joshajohnson/vna/Hardware/Ecal/render.png

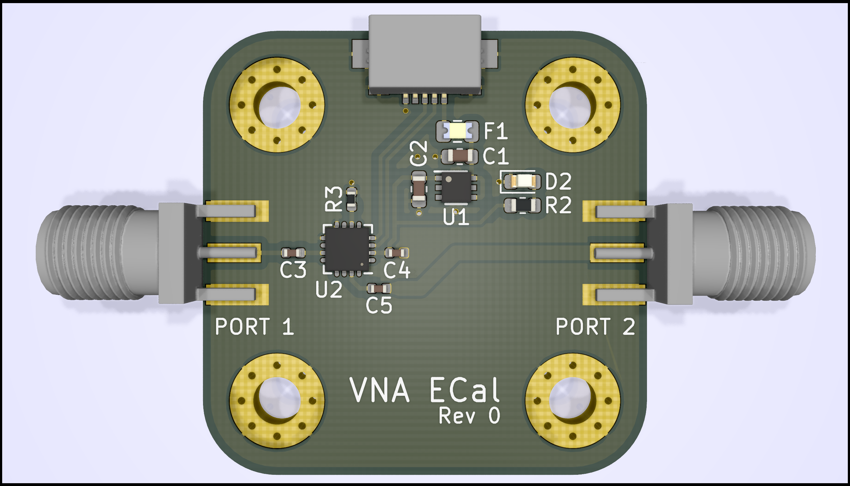
Hardware/Ecal/render.png
