joshajohnson/vna/Hardware/FrontPanel/render.png

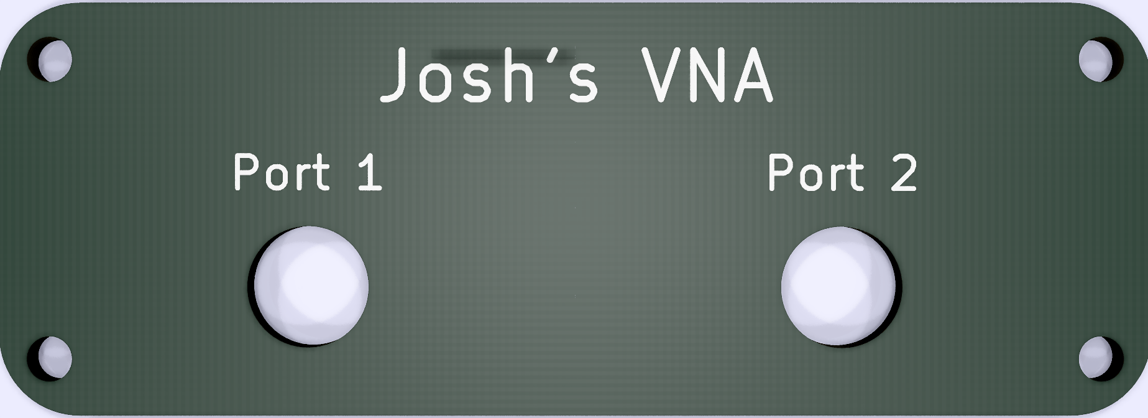
Hardware/FrontPanel/render.png
