joshajohnson/vna/Hardware/RearPanel/render.png

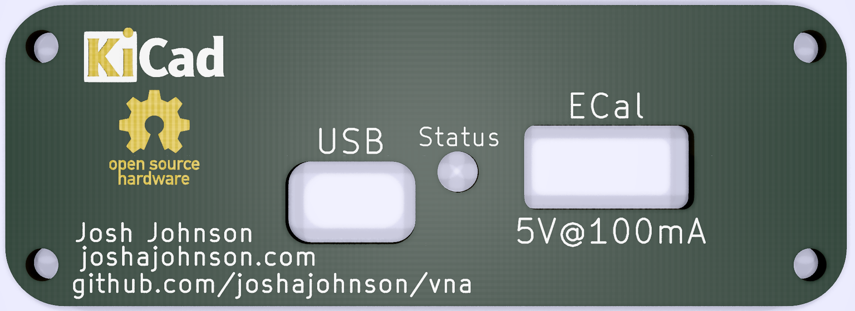
Hardware/RearPanel/render.png
