joshajohnson/vna/Hardware/VNA/svg/couplers-Directional Couplers.png

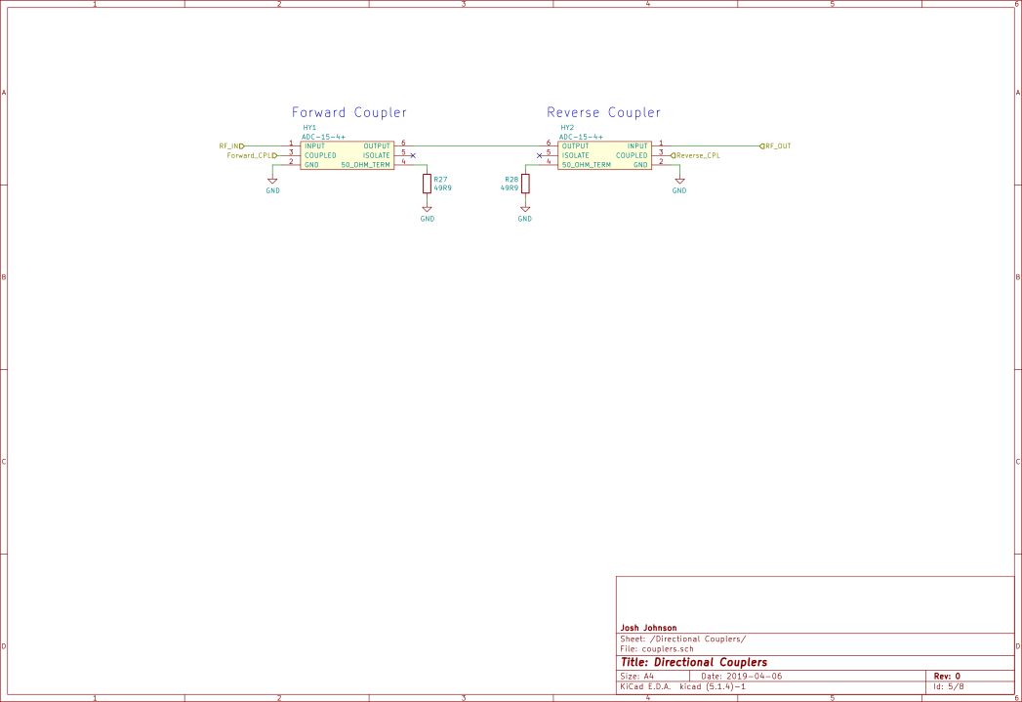
Hardware/VNA/svg/couplers-Directional Couplers.png
