joshajohnson/vna/Hardware/VNA/svg/filterBank-Filter Bank.png

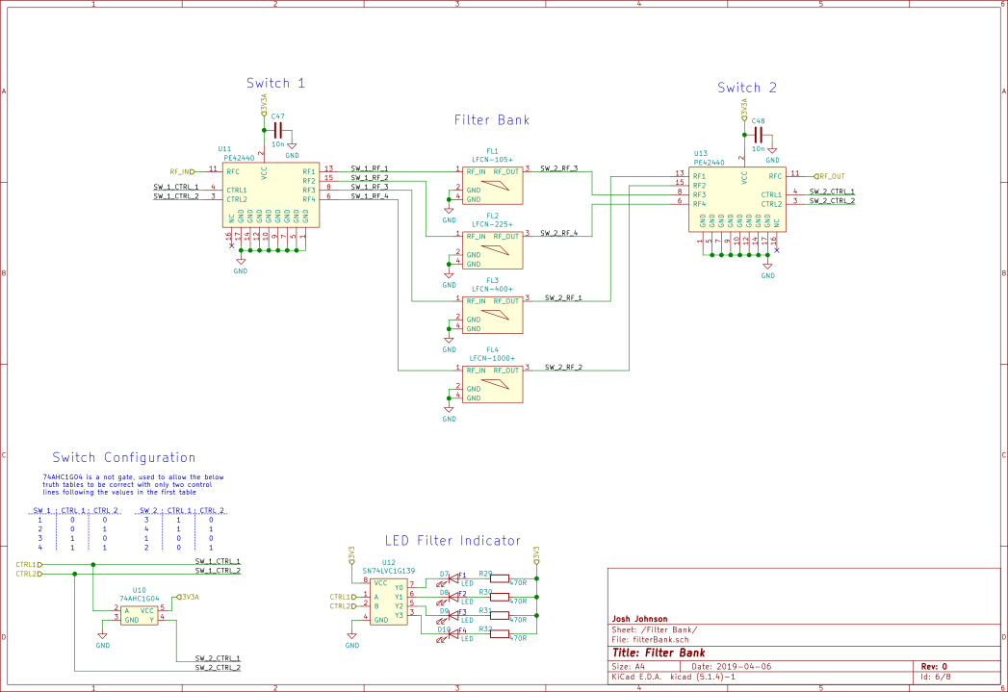
Hardware/VNA/svg/filterBank-Filter Bank.png
