joshajohnson/vna/Hardware/VNA/svg/gainPhaseDetect-Gain Phase Detection.png

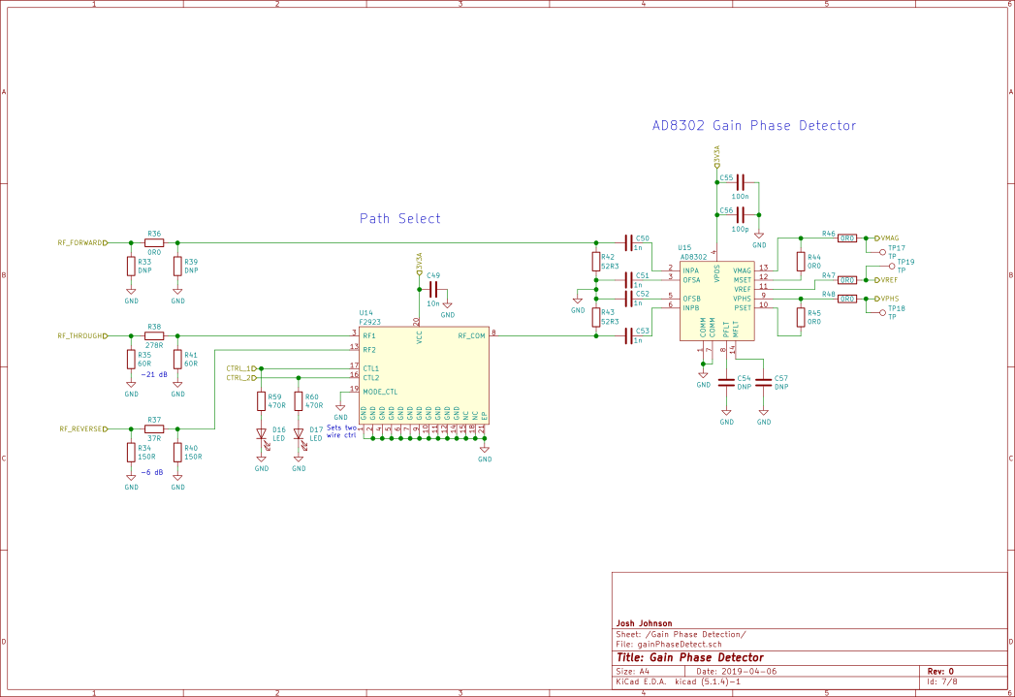
Hardware/VNA/svg/gainPhaseDetect-Gain Phase Detection.png
