joshajohnson/vna/Hardware/VNA/svg/microcontroller-Microcontroller.png

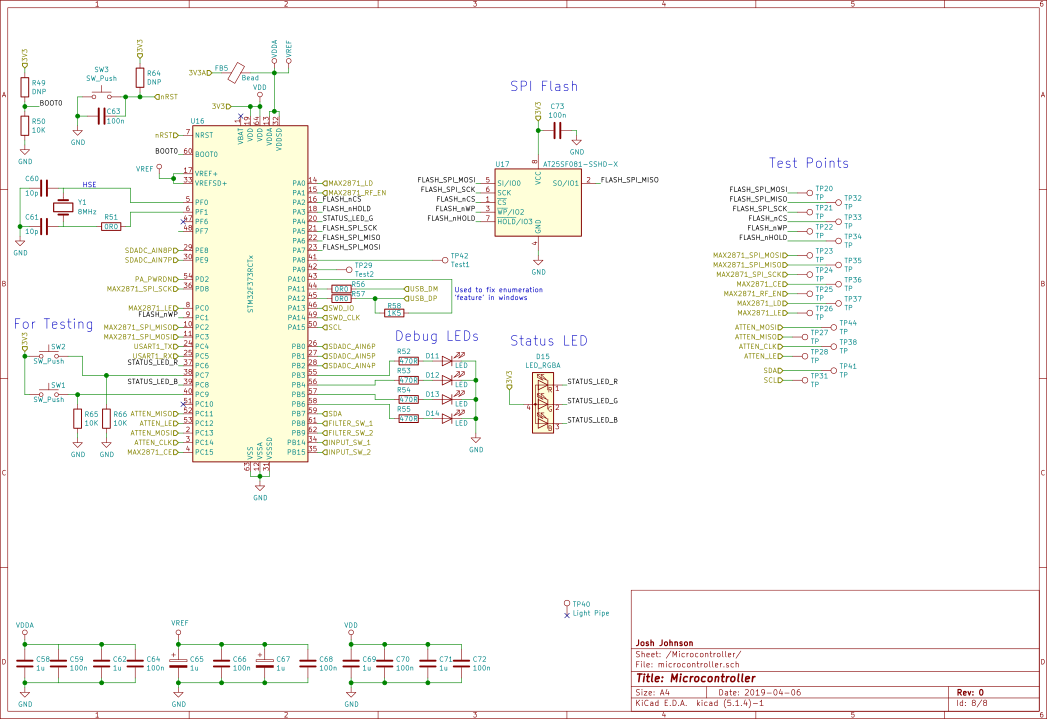
Hardware/VNA/svg/microcontroller-Microcontroller.png
