joshajohnson/vna/Hardware/VNA/svg/power-Power.png

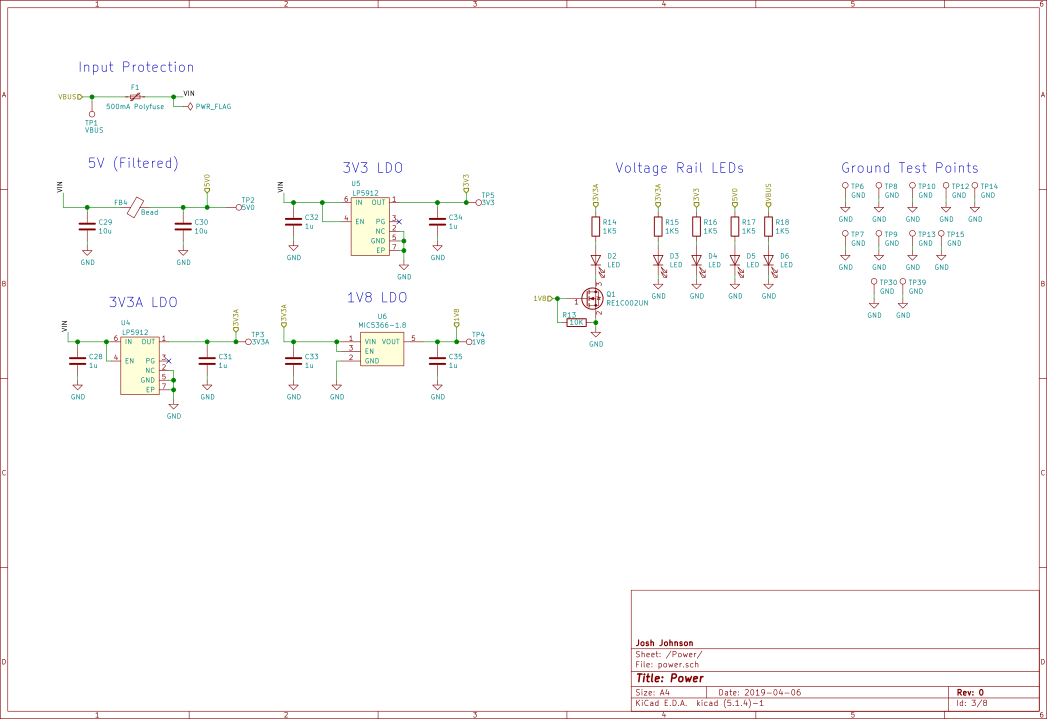
Hardware/VNA/svg/power-Power.png
