joshajohnson/vna/Hardware/VNA/svg/sourceLevel-Source Leveling.png

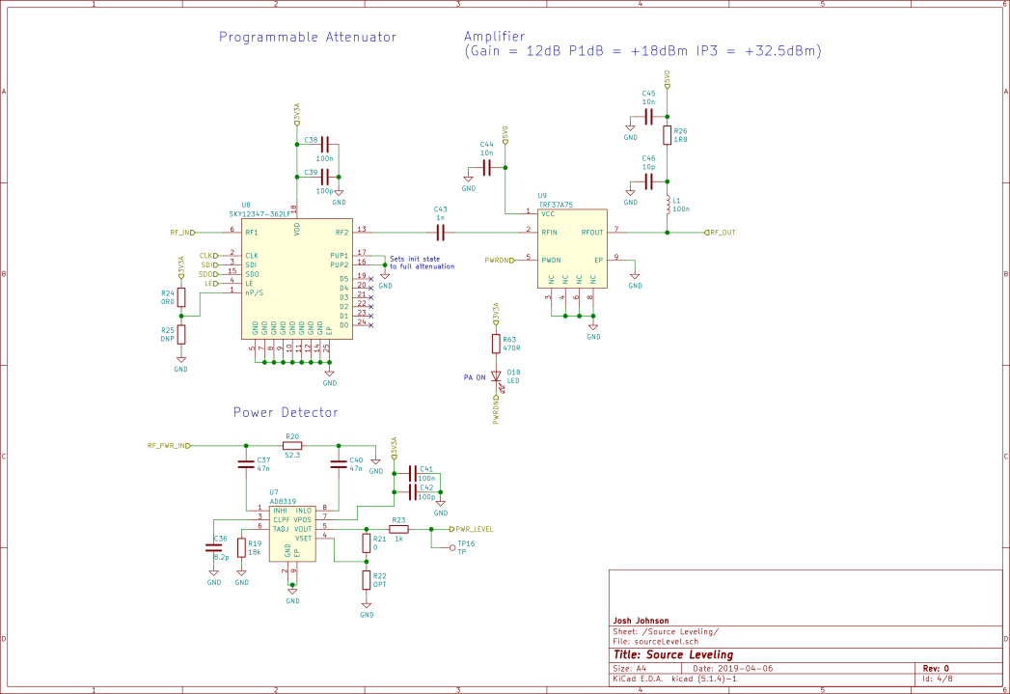
Hardware/VNA/svg/sourceLevel-Source Leveling.png
