joshajohnson/vna/Hardware/VNA/svg/synth-Synth.png

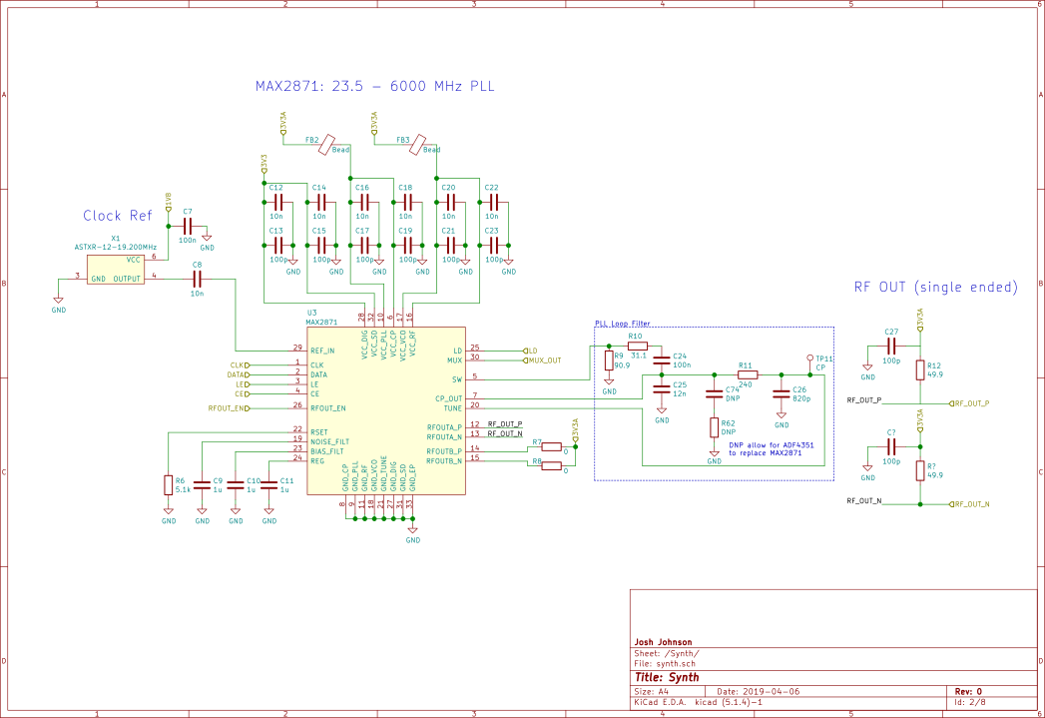
Hardware/VNA/svg/synth-Synth.png
