joshajohnson/vna/Hardware/VNA/svg/VNA.png

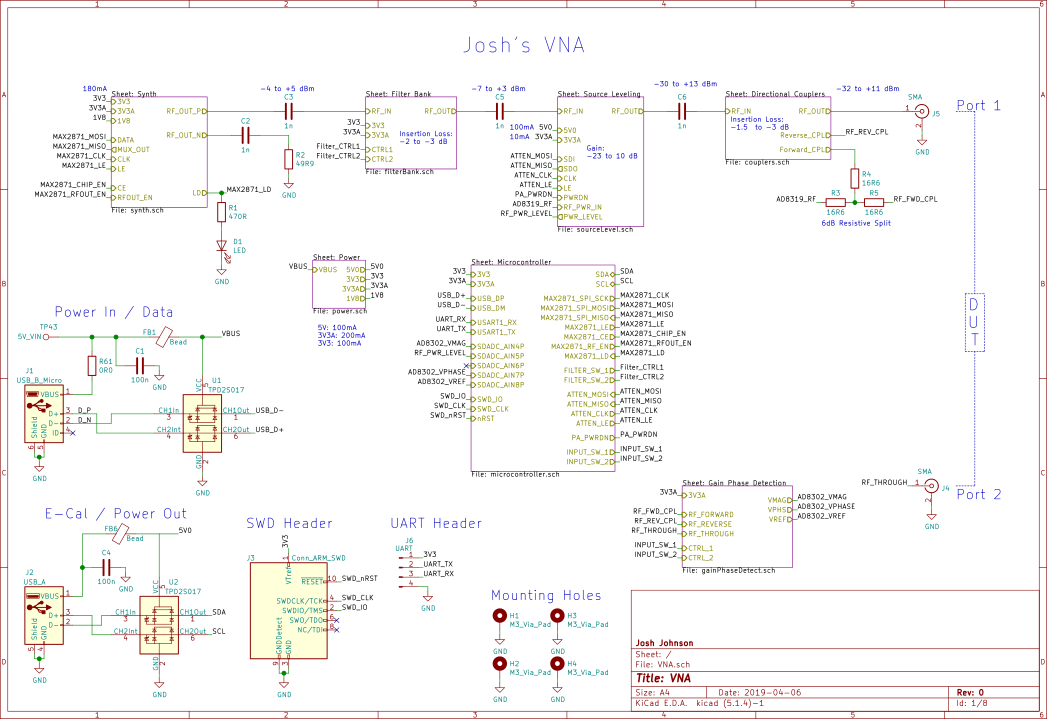
Hardware/VNA/svg/VNA.png
