joshajohnson/vna/Hardware/VNAv0/renders_screenshots/beforeLayoutRender.png

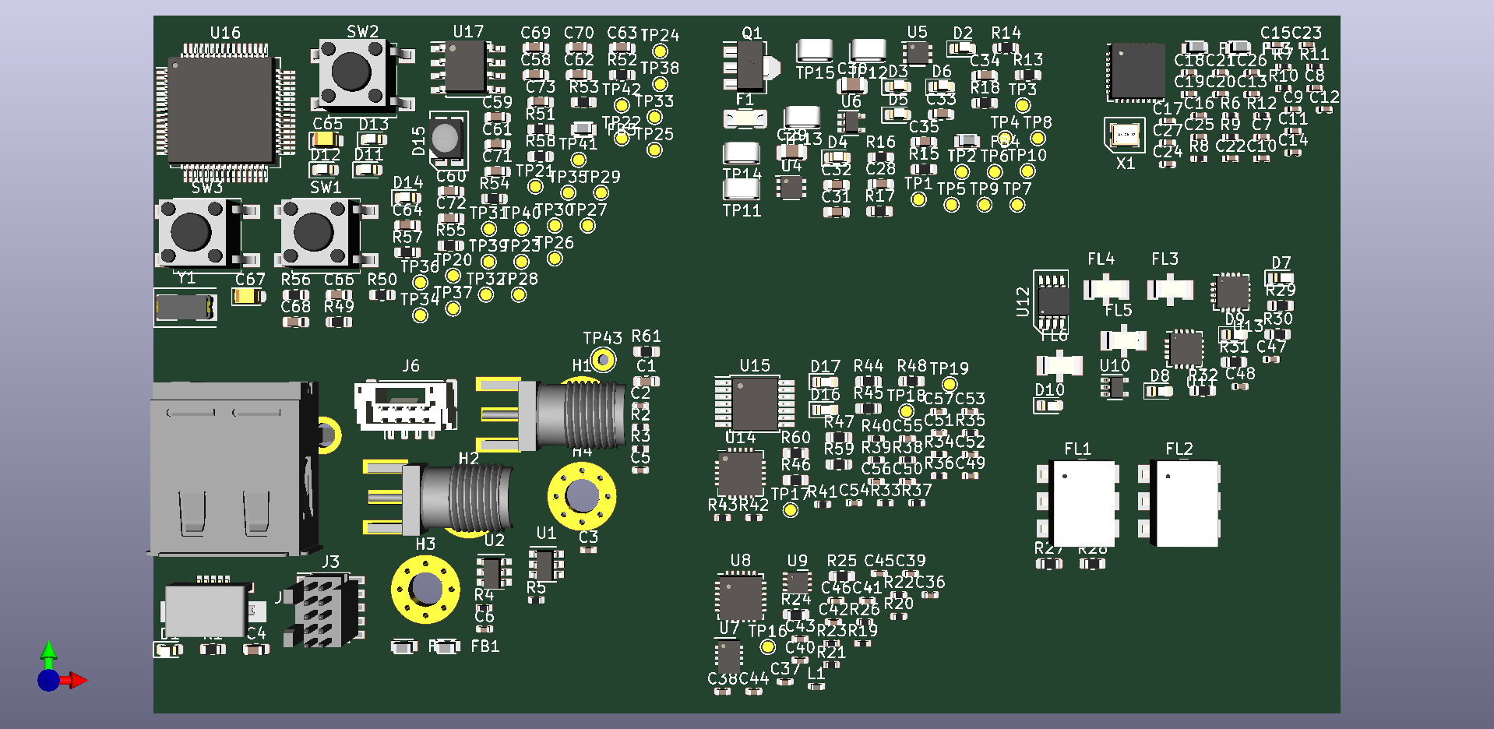
Hardware/VNAv0/renders_screenshots/beforeLayoutRender.png
