joshajohnson/vna/Hardware/VNAv0/renders_screenshots/firstDayRatsNest.PNG

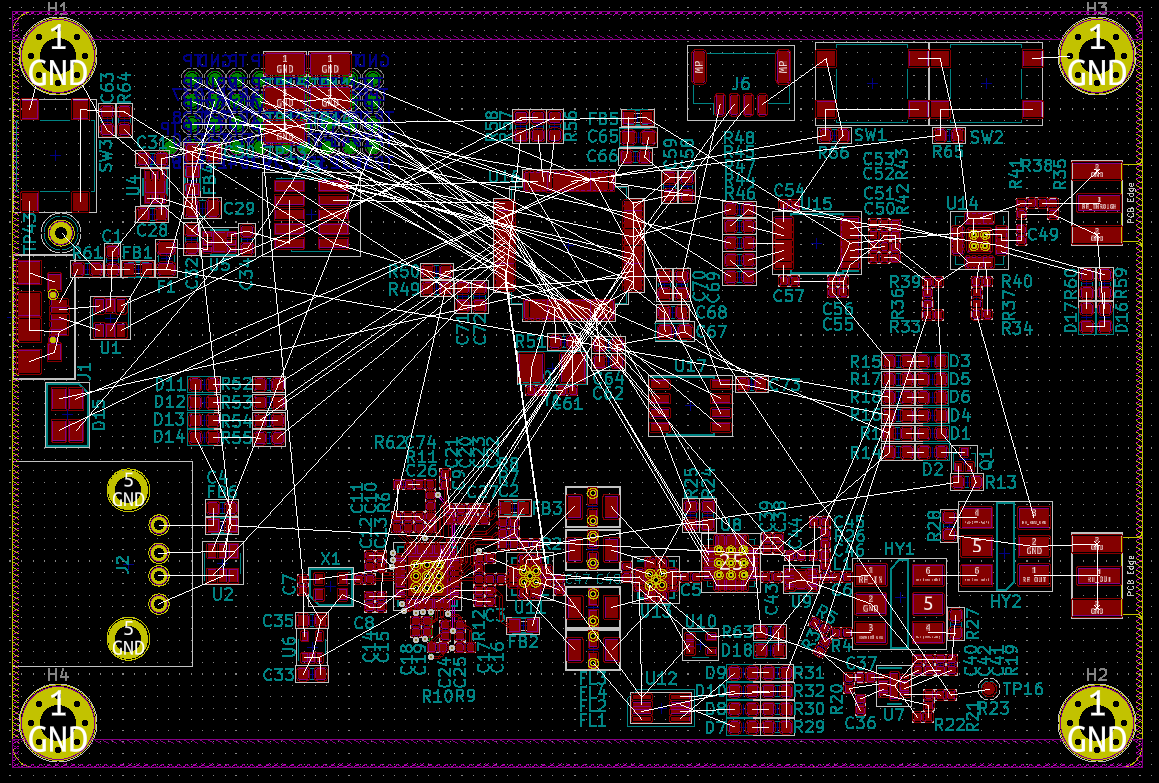
Hardware/VNAv0/renders_screenshots/firstDayRatsNest.PNG
