joshajohnson/vna/Hardware/VNAv0/renders_screenshots/firstDayRender.png

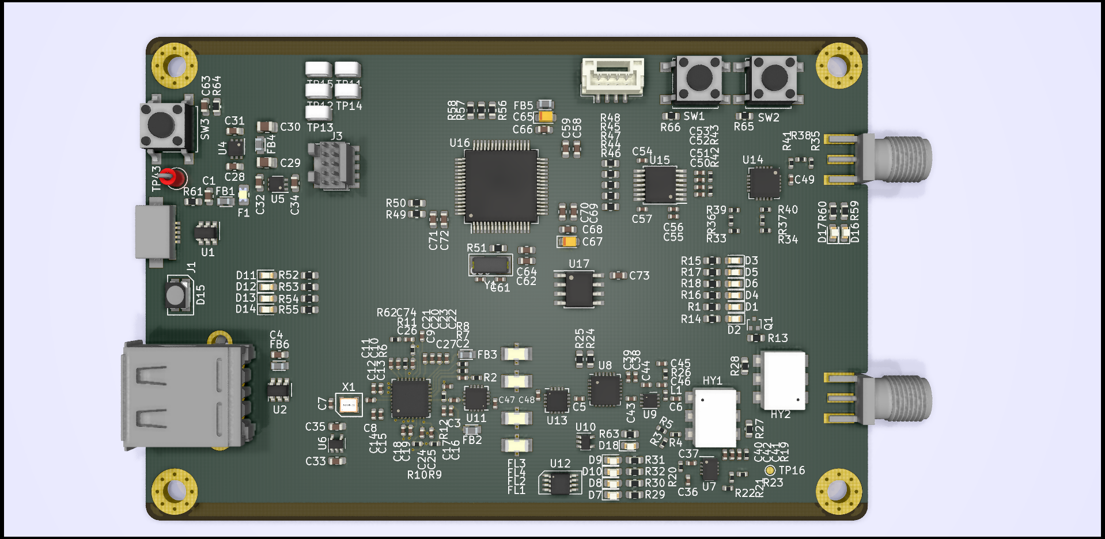
Hardware/VNAv0/renders_screenshots/firstDayRender.png
