joshajohnson/vna/Hardware/VNAv0/renders_screenshots/firstDayRenderEndOn.PNG

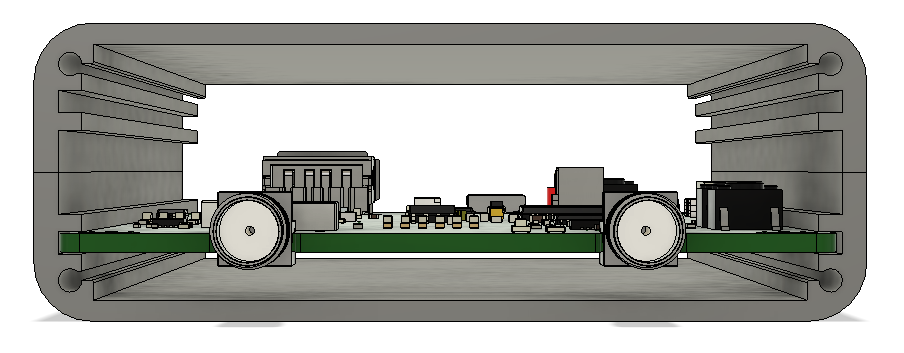
Hardware/VNAv0/renders_screenshots/firstDayRenderEndOn.PNG
