joshajohnson/vna/Hardware/VNAv0/renders_screenshots/firstDayRenderInCase.PNG

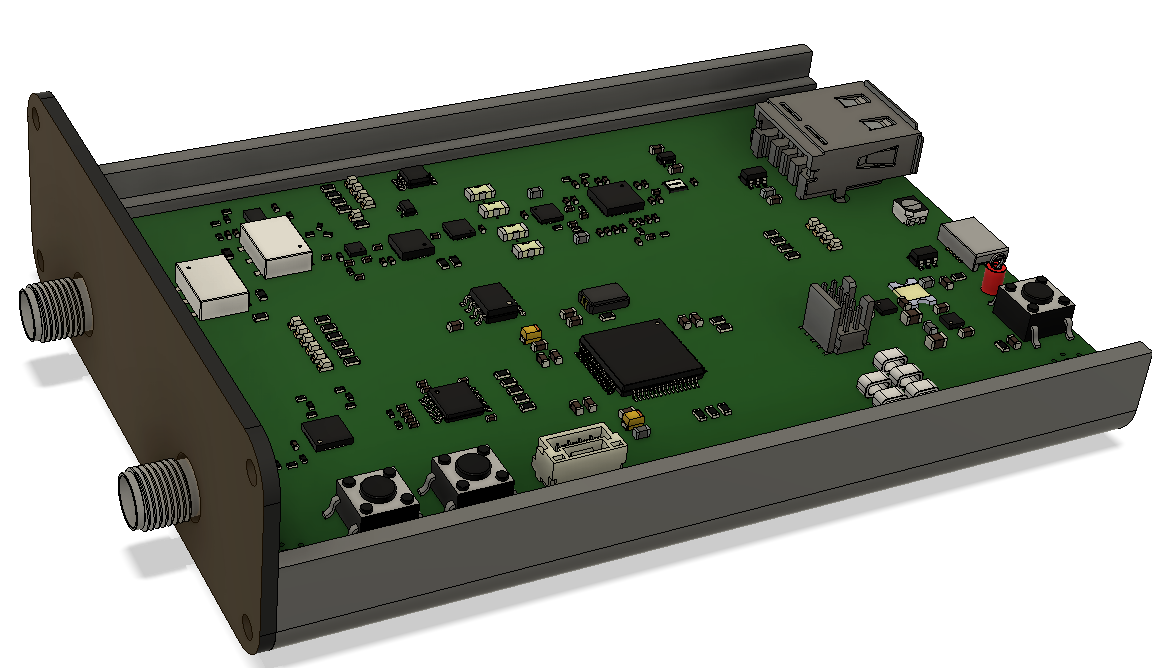
Hardware/VNAv0/renders_screenshots/firstDayRenderInCase.PNG
