joshajohnson/vna/Hardware/VNAv0/renders_screenshots/secondDayRatsNest.PNG

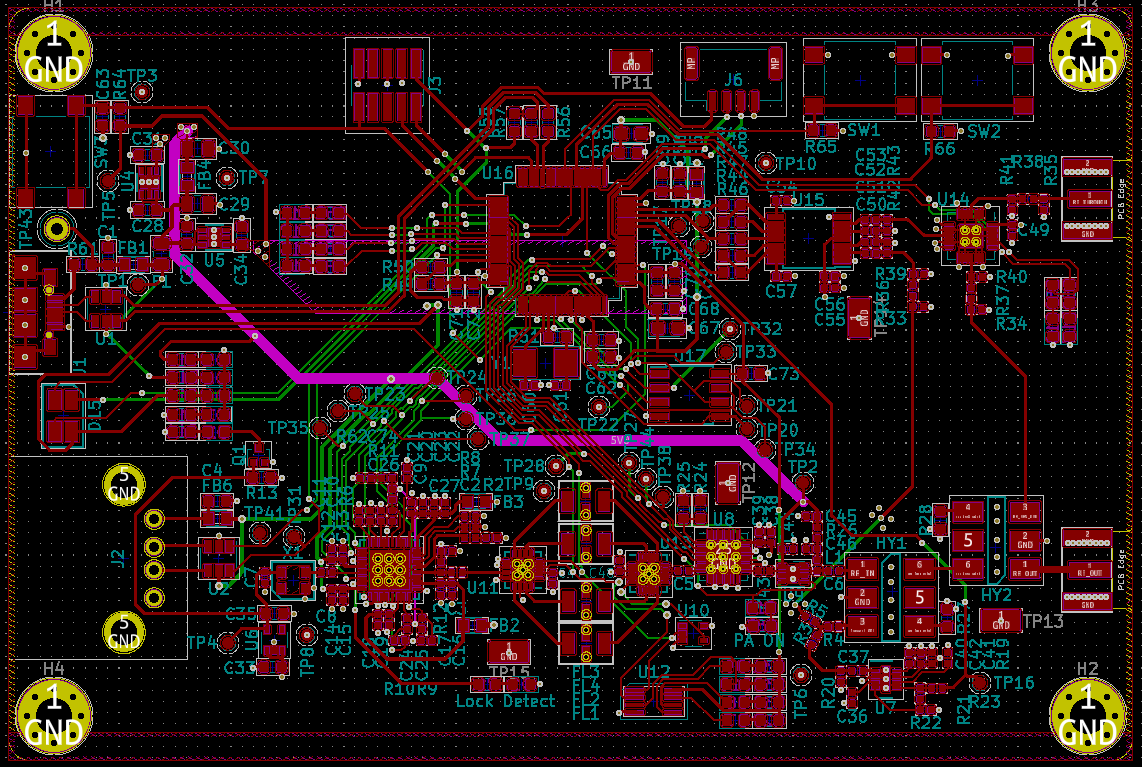
Hardware/VNAv0/renders_screenshots/secondDayRatsNest.PNG
