joshajohnson/vna/Hardware/VNAv0/renders_screenshots/secondDayRender.png

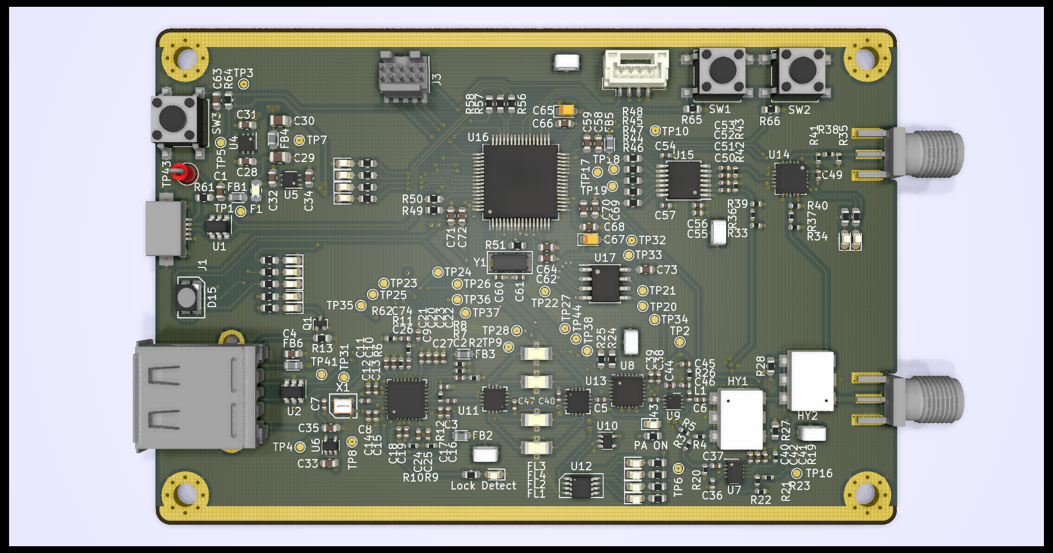
Hardware/VNAv0/renders_screenshots/secondDayRender.png
