joshajohnson/vna/Hardware/VNAv0/renders_screenshots/thirdDayRatsNest.PNG

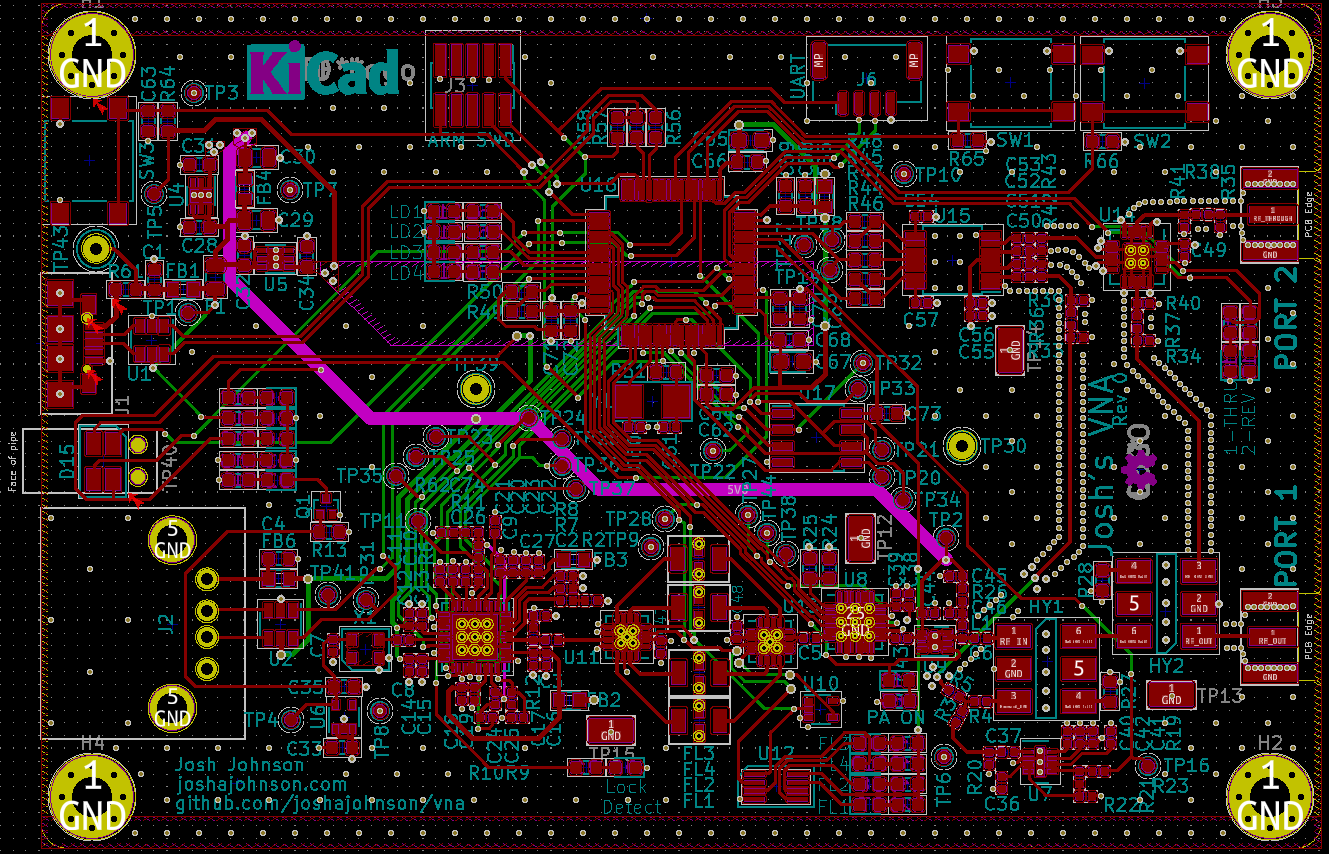
Hardware/VNAv0/renders_screenshots/thirdDayRatsNest.PNG
