joshajohnson/vna/Hardware/VNAv0/renders_screenshots/thirdDayRender.png

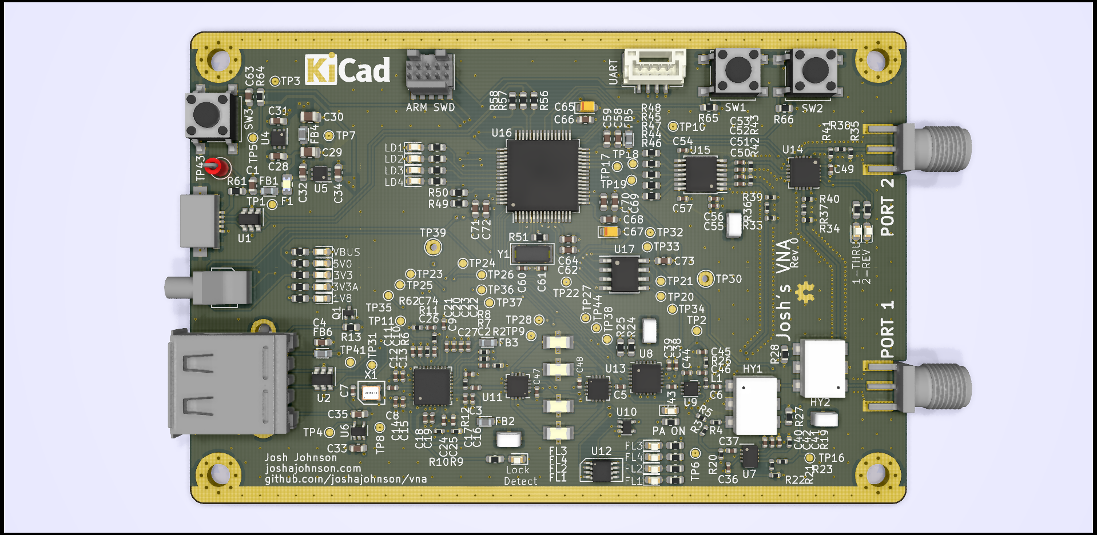
Hardware/VNAv0/renders_screenshots/thirdDayRender.png
