joshajohnson/vna/Hardware/VNAv0/renders_screenshots/thirdDayRenderInCase.PNG

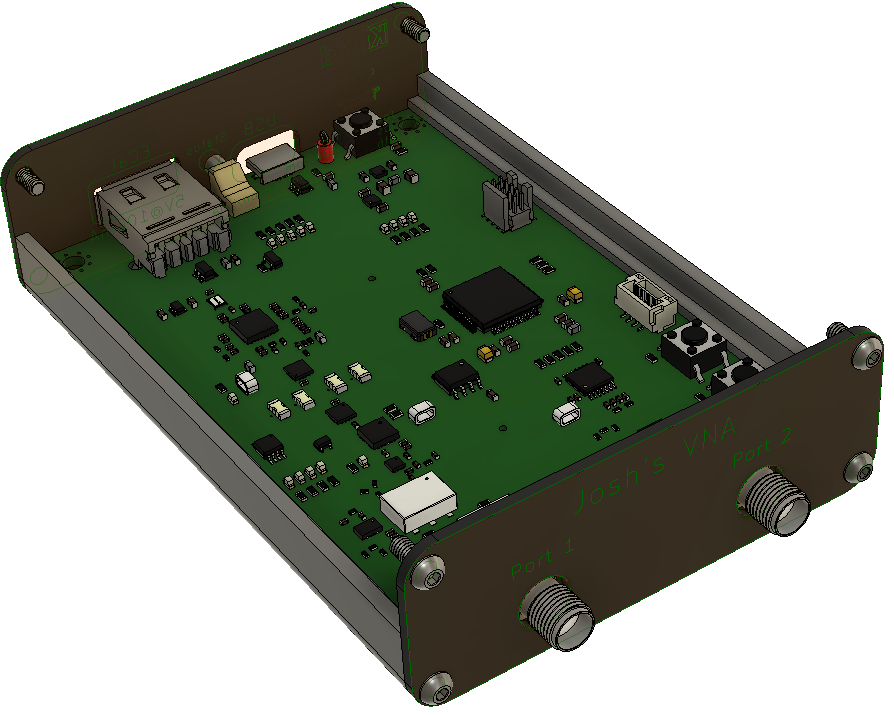
Hardware/VNAv0/renders_screenshots/thirdDayRenderInCase.PNG
