joshajohnson/vna/Thesis/images/rearPanel.PNG

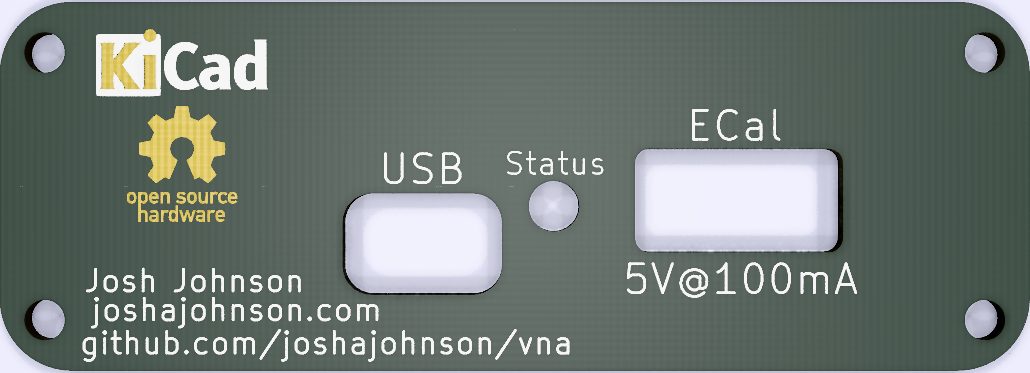
Thesis/images/rearPanel.PNG
