joshajohnson/vna/Thesis/images/vna_max_dev.jpg

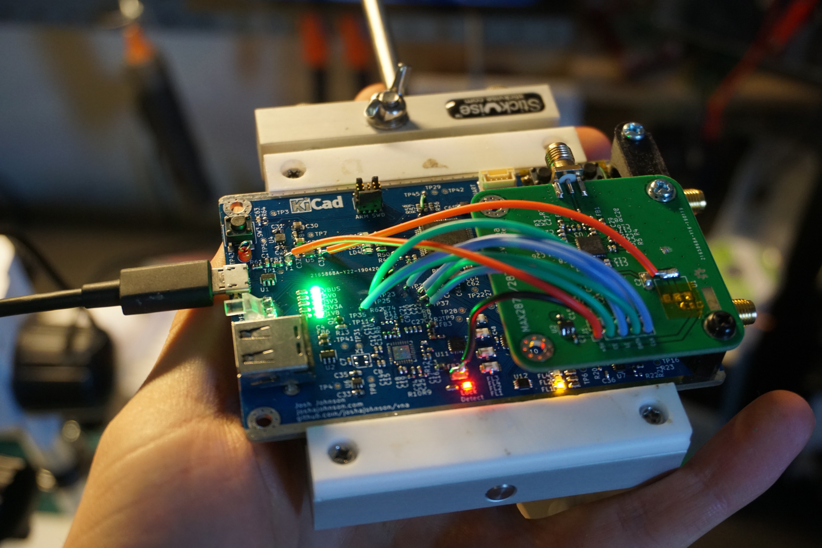
Thesis/images/vna_max_dev.jpg
