joshajohnson/vna/Hardware/Test Boards/ADC-15-4_Dev_Rev_1/3D_Render.jpg

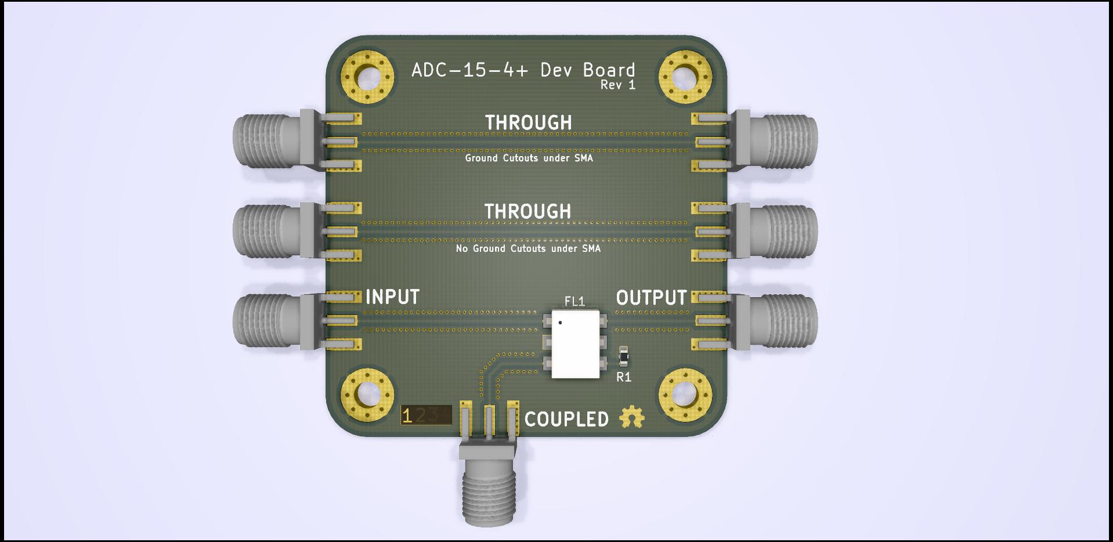
Hardware/Test Boards/ADC-15-4_Dev_Rev_1/3D_Render.jpg
