joshajohnson/vna/Hardware/Test Boards/Combined_Gerbers/Untitled_Combined_Bottom.png

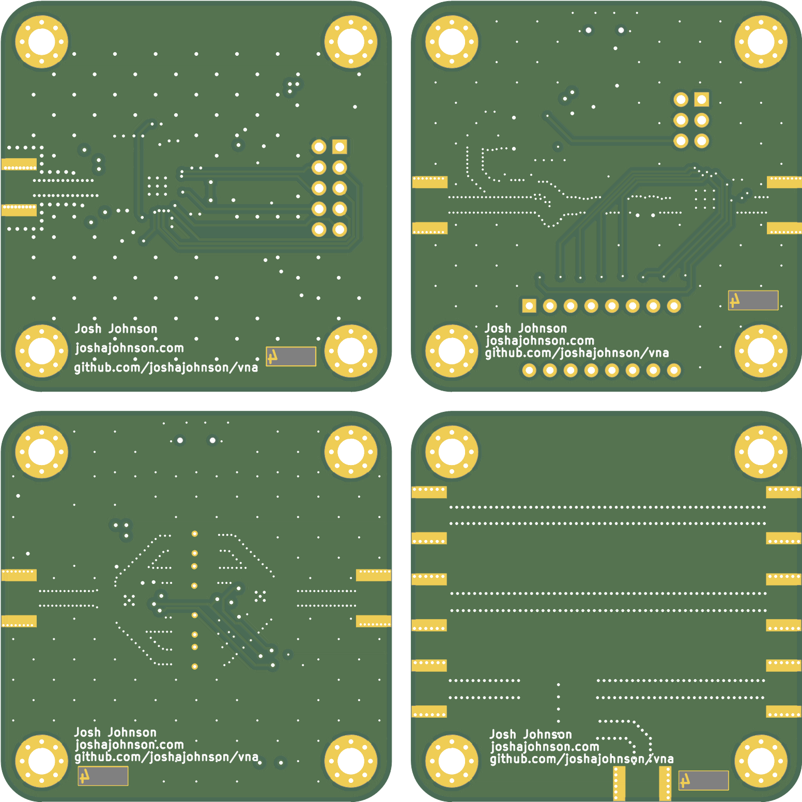
Hardware/Test Boards/Combined_Gerbers/Untitled_Combined_Bottom.png
