joshajohnson/vna/Hardware/Test Boards/Combined_Gerbers/Untitled_Combined_Top.png

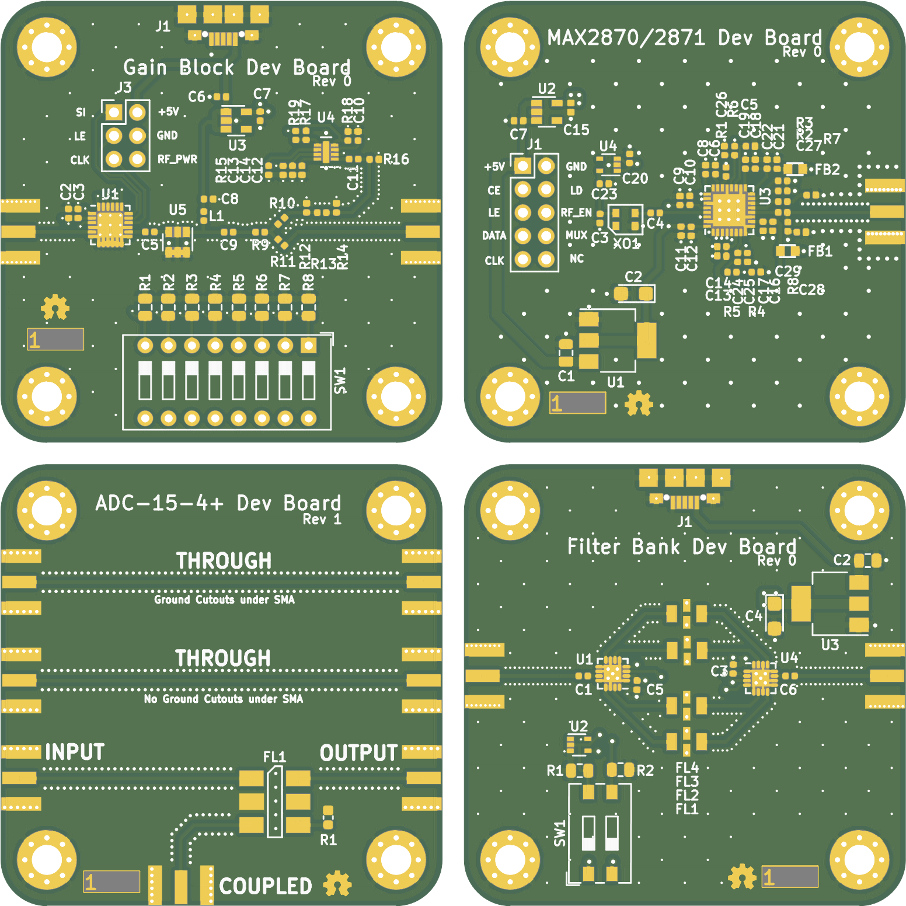
Hardware/Test Boards/Combined_Gerbers/Untitled_Combined_Top.png
