joshajohnson/vna/Hardware/Test Boards/Filter_Bank_Dev_Rev_0/3D_Render.jpg

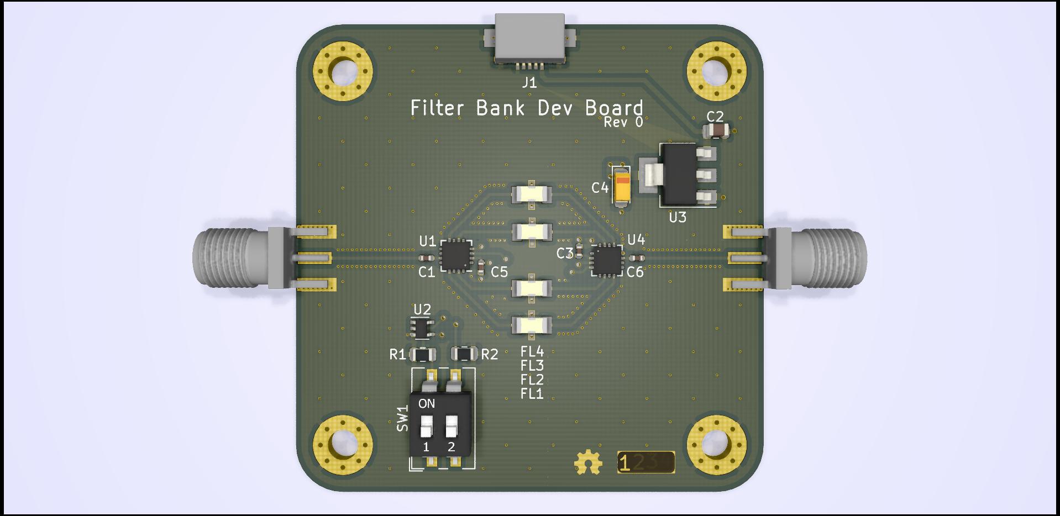
Hardware/Test Boards/Filter_Bank_Dev_Rev_0/3D_Render.jpg
