joshajohnson/vna/Hardware/Test Boards/Gain_Block_Dev_Rev_0/3D_Render.jpg

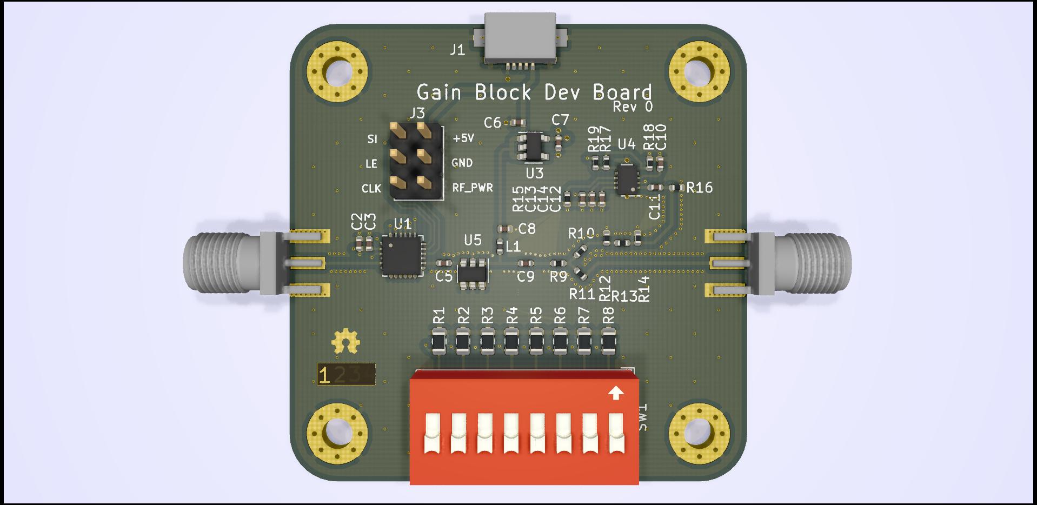
Hardware/Test Boards/Gain_Block_Dev_Rev_0/3D_Render.jpg
