joshajohnson/vna/Hardware/Test Boards/MAX2870_Dev_Rev_0/3D_Render.jpg

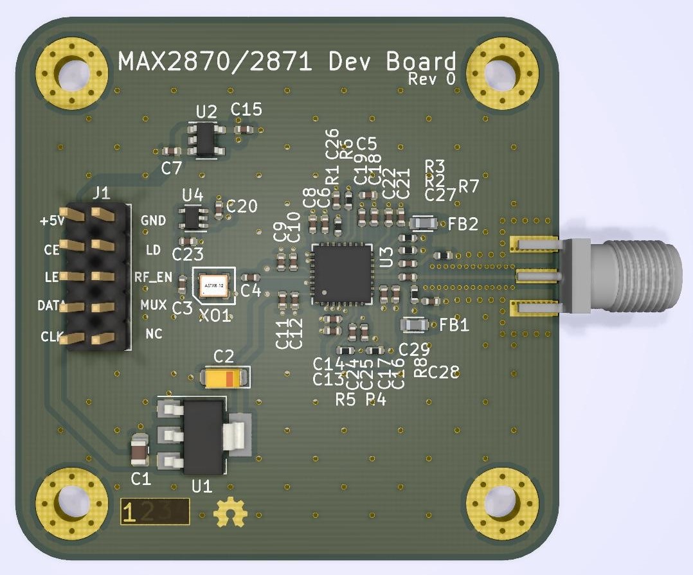
Hardware/Test Boards/MAX2870_Dev_Rev_0/3D_Render.jpg
