joshajohnson/vna/Hardware/Test Boards/TRF37A75_Dev_Rev_0/Render.PNG

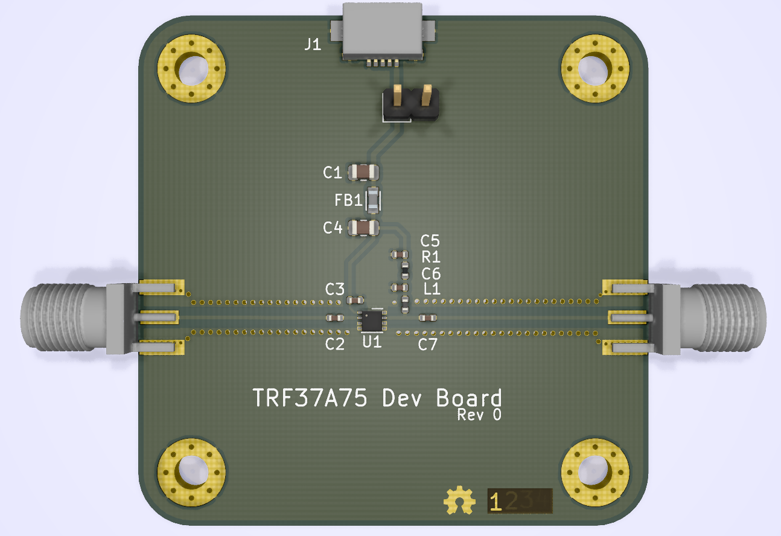
Hardware/Test Boards/TRF37A75_Dev_Rev_0/Render.PNG
