joshajohnson/vna/Software/justTesting/100 MHz LPF.PNG

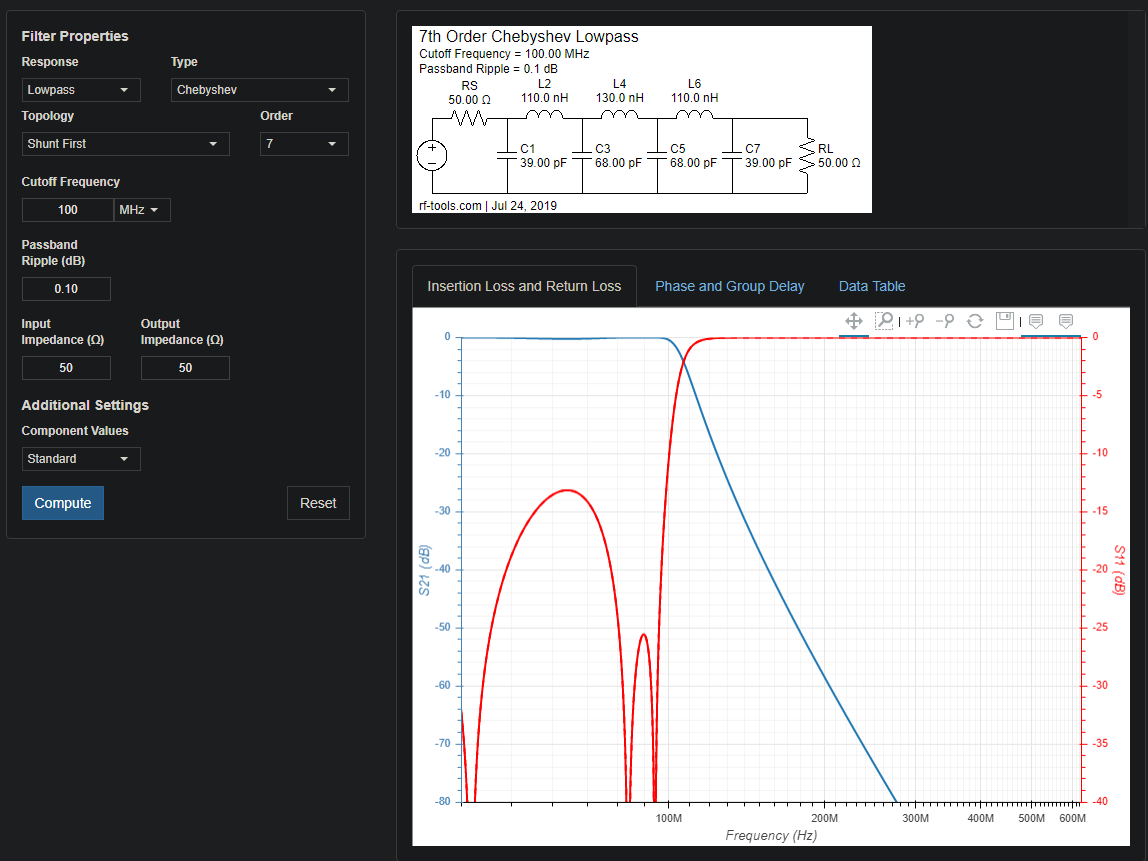
Software/justTesting/100 MHz LPF.PNG
