joshajohnson/vna/Software/justTesting/threeFilters.png

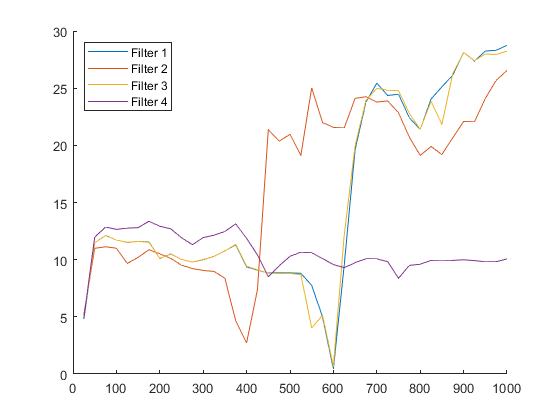
Software/justTesting/threeFilters.png
