joshajohnson/vna/Functionals/Functional Diagram Detailed.pdf

# 25MHz to 1.25GHz VNA Date:

LO | Filter Bank | Source Leveling

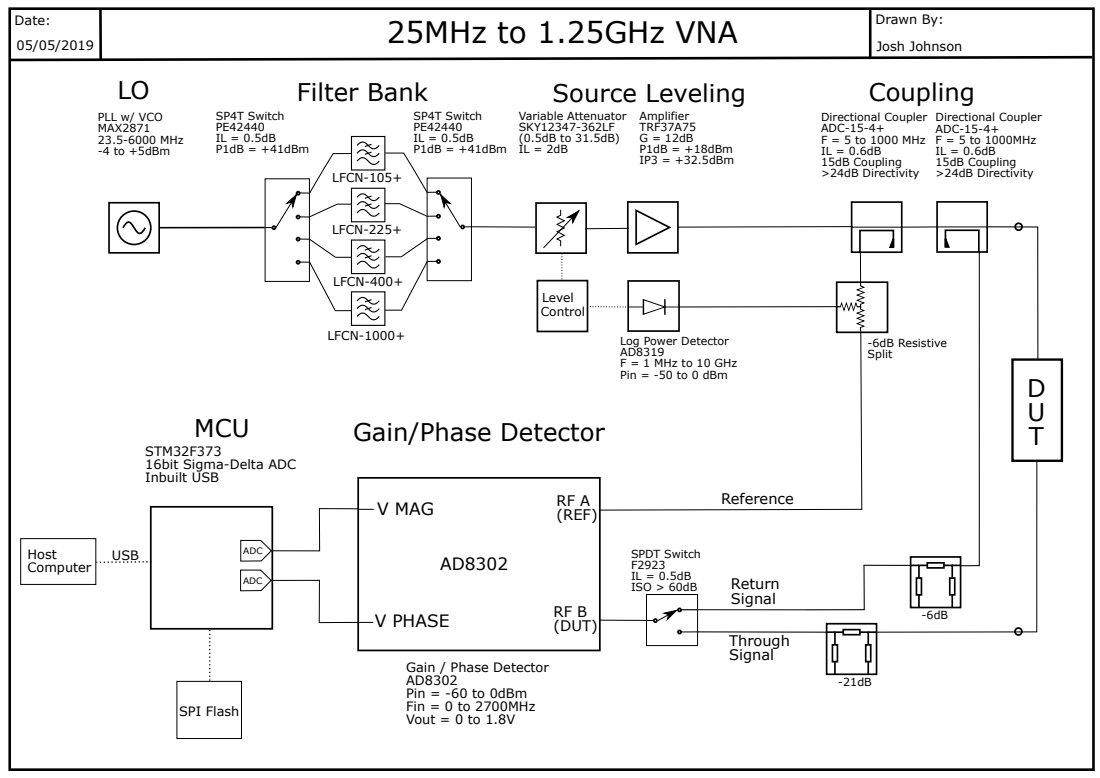
[picture p101: page 1]
Level Control; SPI Flash; Reference; -6dB Resistive Split; Variable Attenuator SKY12347-362LF (0.5dB to 31.5dB) IL = 2dB; Amplifier TRF37A75 G = 12dB P1dB = +18dBm IP3 = +32.5dBm; Directional Coupler ADC-15-4+ F = 5 to 1000 MHz IL = 0.6dB 15dB Coupling >24dB Directivity; Return Signal; Through Signal; ADC; Drawn By:; Josh Johnson; PLL w/ VCO MAX2871 23.5-6000 MHz -4 to +5dBm; Directional Coupler ADC-15-4+ F = 5 to 1000MHz IL = 0.6dB 15dB Coupling >24dB Directivity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

Log Power Detector
F = 1 MHz to 10 GHz
Pin = -50 to 0 dBm

STM32F373
16bit Sigma-Delta ADC
Inbuilt USB

Gain / Phase Detector
Pin = -60 to 0dBm
Fin = 0 to 2700MHz
Vout = 0 to 1.8V
