joshajohnson/vna/Hardware/Test Boards/ADC-15-4_Dev_Rev_0/Schematic.pdf

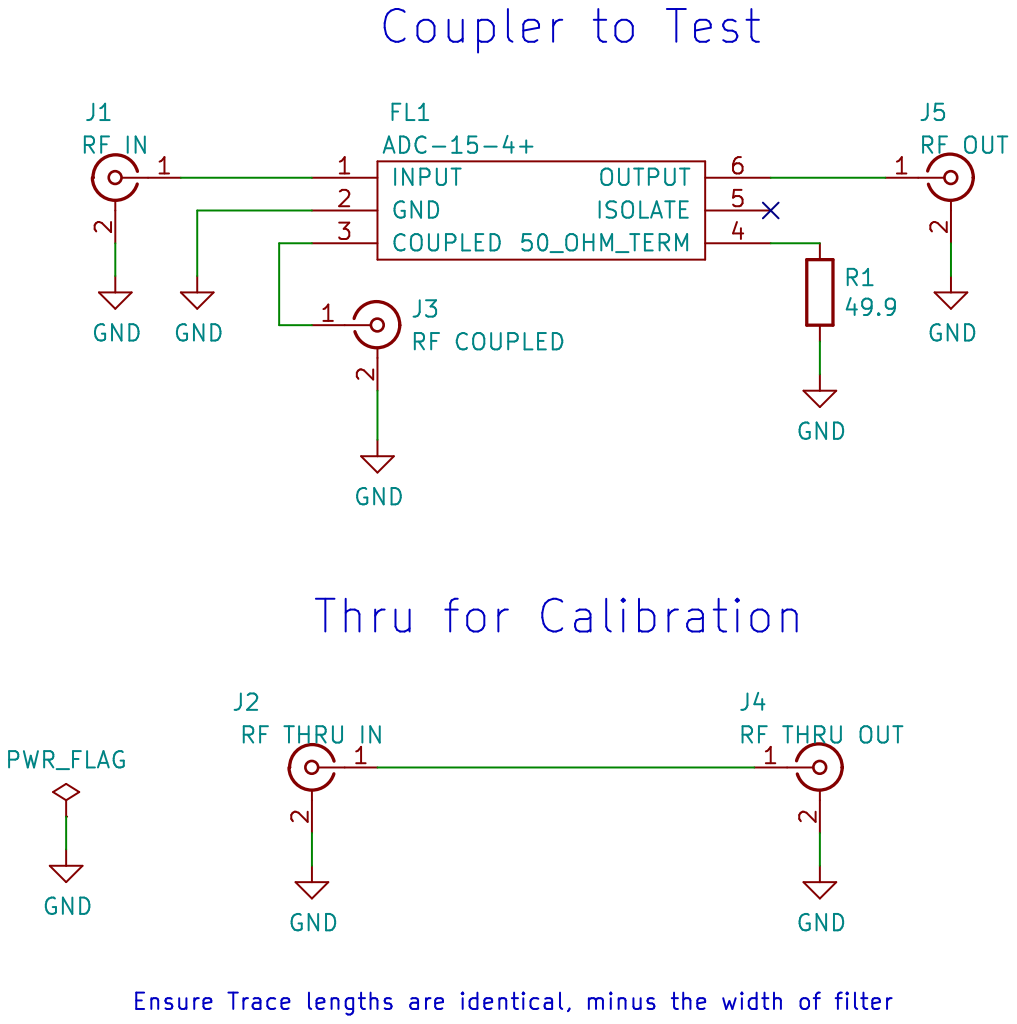
[picture p104: page 1]
