joshajohnson/vna/Firmware/DevBoards/Src/max2871.c

#include "main.h"
#include "max2871.h"
#include "max2871_registers.h"
#include "dwt_stm32_delay.h"
#include <string.h>
#include <stdlib.h>
#include <math.h> // See if this is importing everything

#define MOD 4095
#define STR1_SIZE 128
uint8_t str1[STR1_SIZE] = "";

extern SPI_HandleTypeDef hspi2;
struct MAX2871Struct max2871Status;

void max2871Setup(struct MAX2871Struct *max2871Status)
{
	// Set to inital known state
	max2871ChipEnable(max2871Status);
	max2871RFDisable(max2871Status);
	HAL_GPIO_WritePin(MAX2871_CLK_GPIO_Port, MAX2871_CLK_Pin, 0);
	HAL_GPIO_WritePin(MAX2871_MOSI_GPIO_Port, MAX2871_MOSI_Pin, 0);
	HAL_GPIO_WritePin(MAX2871_MISO_GPIO_Port, MAX2871_MISO_Pin, 0);
	HAL_GPIO_WritePin(MAX2871_LE_GPIO_Port, MAX2871_LE_Pin, 1);

	// Initial writing of registers, with wait time
	max2871RegsInit();

	uint32_t txReg;
	for (int j = 1; j >= 0; j--)
	{
		for (int i = 5; i >= 0; i--)
		{
			txReg = max2871GetRegister(i);
			max2871SpiWrite(txReg);
			if (i == 5) HAL_Delay(20);
		}
		HAL_Delay(20);
	}

	// Set initial register values
	max2871Set_INT(0); 		// Frac N
	max2871Set_N(83);		// Init to 50Mhz
	max2871Set_FRAC(1365);
	max2871Set_CPOC(0);
	max2871Set_CPL(0);
	max2871Set_CPT(0);
	max2871Set_P(1);
	max2871Set_M(4095);
	max2871Set_LDS(1);
	max2871Set_SDN(0);
	max2871Set_MUX(0xC); 	// Reg 6 Readback 0xC
	max2871Set_DBR(1);
	max2871Set_RDIV2(0);
	max2871Set_R(1); 		// 38.4MHz f_PFD
	max2871Set_REG4DB(0);
	max2871Set_CP(15);
	max2871Set_LDF(0);
	max2871Set_LDP(0);
	max2871Set_PDP(1);
	max2871Set_SHDN(0);
	max2871Set_TRI(0);
	max2871Set_RST(0);
	max2871Set_VCO(0);
	max2871Set_VAS_SHDN(0);
	max2871Set_VAS_TEMP(1);
	max2871Set_CSM(0);
	max2871Set_MUTEDEL(1);
	max2871Set_CDM(0);
	max2871Set_CDIV(38);
	max2871Set_SDLDO(0);
	max2871Set_SDDIV(0);
	max2871Set_SDREF(0);
	max2871Set_BS(768);		//BS = fPFD / 50KHz
	max2871Set_FB(1);
	max2871Set_DIVA(6);
	max2871Set_SDVCO(0);
	max2871Set_MTLD(1);
	max2871Set_BDIV(0);
	max2871Set_RFB_EN(0);
	max2871Set_BPWR(0);
	max2871Set_RFA_EN(0);	// Begin with power off
	max2871Set_APWR(0);
	max2871Set_SDPLL(0);
	max2871Set_F01(0);
	max2871Set_LD(1);
	max2871Set_Reserved();

	// Update info in struct
	max2871Status->RFA_EN = 0;
	max2871Status->rfPower = 0;
	// Send updated registers over SPI
	max2871WriteRegisters();
	HAL_Delay(10);
	max2871SetFrequency(50, 0, max2871Status);

	// Check if the PLL has locked
	max2871CheckLD(max2871Status);
}

void max2871SpiWrite(uint32_t r)
{
	uint8_t txData[4];
	// Move bits around to deal with the little endiness on the STM32
	txData[0] = r >> 24;
	txData[1] = (r & 0xff0000) >> 16 ;
	txData[2] = (r & 0xff00) >> 8;
	txData[3] = (r & 0xff);

	// Ensure LE high
	HAL_GPIO_WritePin(MAX2871_LE_GPIO_Port, MAX2871_LE_Pin, 1);
	DWT_Delay_us(1);
	// Start by bringing LE low
	HAL_GPIO_WritePin(MAX2871_LE_GPIO_Port, MAX2871_LE_Pin, 0);

	// Transmit all the bits!
	HAL_SPI_Transmit(&hspi2, (uint8_t *) txData, 4, 50);

	// Once Transfer complete, pull LE high
	while (HAL_SPI_GetState(&hspi2) != HAL_SPI_STATE_READY);
	HAL_GPIO_WritePin(MAX2871_LE_GPIO_Port, MAX2871_LE_Pin, 1);
}

uint32_t max2871SpiRead(void)
{
	uint8_t data[4];
	uint32_t dataReturn;

	max2871SpiWrite(0x06);

	// Ensure LE High
	HAL_GPIO_WritePin(MAX2871_LE_GPIO_Port, MAX2871_LE_Pin, 1);

	HAL_SPI_Receive(&hspi2, (uint8_t *) data, 4, 1000);

	dataReturn = (data[0] << 24) | (data[1] << 16) | (data[2] << 8) | (data[3]);

	return dataReturn;
}

void max2871WriteRegisters(void)
{
	for (int i = 5; i >= 0; i--)
	{
		max2871SpiWrite(max2871GetRegister(i));
	}
}

float max2871SetFrequency(float mhz, uint8_t intN, struct MAX2871Struct *max2871Status)
{
	uint8_t  diva;
	// Determine DIVA
	if (mhz < 23.5)
		return -1;
	else if (mhz < 46.875)
		diva = 7;
	else if (mhz < 93.75)
		diva = 6;
	else if (mhz < 187.5)
		diva = 5;
	else if (mhz < 375)
		diva = 4;
	else if (mhz < 750)
		diva = 3;
	else if (mhz < 1500)
		diva = 2;
	else if (mhz < 3000)
		diva = 1;
	else if (mhz < 6000)
		diva = 0;
	else
		return -1;

	// Calculate fOUT
	float fComp = 38.4;
	float fVCO = mhz * (2 << (diva - 1));
	float n = fVCO / fComp;
	uint32_t N = (uint16_t) n;

	float F = round((n - N) * MOD);

	if (intN == 1)
		fVCO = N * fComp;
	else if (!intN)
		fVCO = (N + (F/MOD)) * fComp;

	float fOUT = fVCO / (2 << (diva - 1));

	// Set registers for Int-N configuration
	if (intN == 1)
	{
		max2871Set_INT(1);
		max2871Set_N(N);
		max2871Set_FRAC(F);
		max2871Set_CPL(0);
		max2871Set_M(MOD);
		max2871Set_LDF(1);
		max2871Set_DIVA(diva);
		max2871Set_F01(0);
	}
	// Set registers for Frac-N configuration
	else if (!intN)
	{
		max2871Set_INT(0);
		max2871Set_N(N);
		max2871Set_FRAC(F);
		max2871Set_CPL(1);
		max2871Set_M(MOD);
		max2871Set_LDF(0);
		max2871Set_DIVA(diva);
		max2871Set_F01(1);
	}
	max2871Status->intN_nFracN = intN;
	max2871Status->frequency = fOUT;
	max2871WriteRegisters();

	return fOUT;
}

void max2871ChipEnable(struct MAX2871Struct *max2871Status)
{
	HAL_GPIO_WritePin(MAX2871_CE_GPIO_Port, MAX2871_CE_Pin, 1);
	max2871Status->CHIP_EN = 1;
}

void max2871ChipDisable(struct MAX2871Struct *max2871Status)
{
	HAL_GPIO_WritePin(MAX2871_CE_GPIO_Port, MAX2871_CE_Pin, 0);
	max2871Status->CHIP_EN = 0;
}

void max2871RFEnable(struct MAX2871Struct *max2871Status)
{
	max2871Set_RFA_EN(1);
	HAL_GPIO_WritePin(MAX2871_RFOUTEN_GPIO_Port, MAX2871_RFOUTEN_Pin, 1);
	max2871Status->RFA_EN = 1;
	max2871Status->RF_CHIP_EN = 1;
	max2871WriteRegisters();
}

void max2871RFDisable(struct MAX2871Struct *max2871Status)
{
	max2871Set_RFA_EN(0);
	HAL_GPIO_WritePin(MAX2871_RFOUTEN_GPIO_Port, MAX2871_RFOUTEN_Pin, 0);
	max2871Status->RFA_EN = 0;
	max2871Status->RF_CHIP_EN = 0;
	max2871WriteRegisters();
}

int8_t max2871SetPower(int8_t dbm, struct MAX2871Struct *max2871Status)
{
	switch (dbm)
	{
		case -4:
			max2871Status->rfPower = 0;
			break;

		case -1:
			max2871Status->rfPower = 1;
			break;

		case 2:
			max2871Status->rfPower = 2;
			break;

		case 5:
			max2871Status->rfPower = 3;
			break;

		default:
			// Don't change anything, and return an error
			return -1;
	}

	max2871Set_APWR(max2871Status->rfPower);
	max2871WriteRegisters();

	return max2871Status->rfPower;
}

void max2871CheckLD(struct MAX2871Struct *max2871Status)
{
	uint8_t state = HAL_GPIO_ReadPin(MAX2871_LD_GPIO_Port, MAX2871_LD_Pin);
	max2871Status->ldState = state;
}

void max2871PrintRegisters(void)
{
	uint32_t txReg;

	for (int8_t i = 0; i <= 5; i++)
	{
		txReg = max2871GetRegister(i);
		sprintf((char *)str1, "Register %d = 0x%x\n", i, (unsigned int) txReg);
		printUSB(str1);
		HAL_Delay(10);

	}

	txReg = max2871SpiRead();
	sprintf((char *)str1, "Register 6 = 0x%x\n\n", (unsigned int) txReg);
	printUSB(str1);
}

void max2871PrintStatus(struct MAX2871Struct *max2871Status)
{
	uint8_t str1[128] = "";
	int8_t powerArray[4] = {-4, -1, 2, 5};

	printUSB("----  MAX2871  ----\n\n");

	sprintf((char *)str1, "Chip Enable = %d\n", max2871Status->CHIP_EN);
	printUSB(str1);

	max2871CheckLD(max2871Status);
	sprintf((char *)str1, "LD Status = %d\n", max2871Status->ldState);
	printUSB(str1);

	sprintf((char *)str1, "Set Frequency = %0.2f MHz\n", max2871Status->frequency);
	printUSB(str1);

	sprintf((char *)str1, "Int-N / nFrac-N = %d\n", max2871Status->intN_nFracN);
	printUSB(str1);

	sprintf((char *)str1, "RFA Enable = %d\n", max2871Status->RFA_EN);
	printUSB(str1);

	sprintf((char *)str1, "RF Out Enable = %d\n", max2871Status->RF_CHIP_EN);
	printUSB(str1);

	sprintf((char *)str1, "RF Power = %d dBm\n", powerArray[max2871Status->rfPower]);
	printUSB(str1);

	max2871PrintRegisters();

	printUSB("\n");
}

void setFrequncyUSB(struct MAX2871Struct *max2871Status)
{
	uint8_t str1[64] = "";
	double frequency;
	printUSB("Enter a frequency between 23.5 and 6000 MHz: ");
	scanUSB(str1, 64);
	frequency = atof(str1);
	printUSB(str1);

	if (frequency < 23.5)
	{
		printUSB("\nFrequency too low. \n\n");
	}
	else if (frequency > 6000)
	{
		printUSB("\nFrequency too high. \n\n");
	}

	else if ((frequency >= 23.5) && (frequency <= 6000))
	{
		sprintf((char *)str1, "\nFrequency: %0.2f MHz\n\n", frequency);
		printUSB(str1);

		max2871SetFrequency(frequency, max2871Status->intN_nFracN, max2871Status);
	}
	else
	{
		printUSB("\nBad input, try harder next time.\n\n");
	}

}

void setIntFracUSB(struct MAX2871Struct *max2871Status)
{
	uint8_t str1[64] = "";

	printUSB("Enter int for Int-N mode, frac for Frac-N mode: ");
	scanUSB(str1, 64);

	if (strcmp(str1, "F") == 0 || strcmp(str1, "f") == 0 || strcmp(str1, "frac") == 0 || strcmp(str1, "Frac") == 0)
	{
		printUSB(str1);
		max2871SetFrequency(max2871Status->frequency, 0, max2871Status);
		printUSB("\nFractional-N mode set\n\n");
	}
	else if (strcmp(str1, "I") == 0 || strcmp(str1, "i") == 0 || strcmp(str1, "int") == 0 || strcmp(str1, "Int") == 0)
	{
		printUSB(str1);
		max2871SetFrequency(max2871Status->frequency, 0, max2871Status);
		printUSB("\nInteger-N mode set\n\n");
	}
	else
	{
		printUSB(str1);
		printUSB("\nBad input, try harder next time.\n\n");
	}

}

void setMaxPowerUSB(struct MAX2871Struct *max2871Status)
{
	uint8_t str1[64] = "";
	int8_t power;
	printUSB("Choose MAX2871 output power from -4, -1, 2, 5 dBm: ");
	scanUSB(str1, 64);
	power = atoi(str1);

	if (power == -4 || power == -1 || power == 2 || power == 5)
	{
		printUSB(str1);
		printUSB("\n\n");
		max2871SetPower(power, max2871Status);
	}
	else
	{
		printUSB(str1);
		printUSB("\nBad input, try harder next time.\n\n");
	}
}

void rfEnableDisableUSB(struct MAX2871Struct *max2871Status)
{
	uint8_t str1[64] = "";

	printUSB("Enter enable to enable RF output, enter disable to disable RF output: ");
	scanUSB(str1, 64);
	printUSB(str1);

	if (strcmp(str1, "enable") == 0 || strcmp(str1, "en") == 0 || strcmp(str1, "e") == 0 || strcmp(str1, "E") == 0)
	{
		max2871RFEnable(max2871Status);
		printUSB("\nRF output enabled\n\n");
	}
	else if (strcmp(str1, "disable") == 0 || strcmp(str1, "dis") == 0 || strcmp(str1, "d") == 0 || strcmp(str1, "D") == 0)
	{
		max2871RFDisable(max2871Status);
		printUSB("\nRF output disabled\n\n");
	}
	else
	{
		printUSB("\nBad input, try harder next time.\n\n");
	}
}

void max2871Sweep(float lowerFreq, float higherFreq, float numSteps, float sweepTime, uint8_t rampUp, struct MAX2871Struct *max2871Status)
{

	if (rampUp)
	{
		float stepSize = ((higherFreq - lowerFreq) / numSteps);
		uint32_t delay = sweepTime * 1000000 / numSteps; 	// Delay is in uS


		float currentFrequency = lowerFreq;
		max2871SetFrequency(currentFrequency,0,max2871Status);

		while (currentFrequency < higherFreq)
		{
			DWT_Delay_us(delay);
			currentFrequency += stepSize;
			max2871SetFrequency(currentFrequency,0,max2871Status);
		}
	}
	else
	{
		float stepSize = ((higherFreq - lowerFreq) / numSteps);
		uint32_t delay = sweepTime * 1000000 / numSteps; 	// Delay is in uS


		float currentFrequency = higherFreq;
		max2871SetFrequency(currentFrequency,0,max2871Status);

		while (currentFrequency > lowerFreq)
			{
				DWT_Delay_us(delay);
				currentFrequency -= stepSize;
				max2871SetFrequency(currentFrequency,0,max2871Status);
			}
	}

}

void max2871SweepUSB(struct MAX2871Struct *max2871Status)
{
	uint8_t str1[64] = "";
	uint8_t error = 0;

	printUSB("--- Sweep Config --- \n\n");

	printUSB("Enter Lower Frequency in MHz: ");
	scanUSB(str1, 64);
	printUSB(str1);
	printUSB("\n");
	float lowerFreq = (float) atof(str1);
	if (lowerFreq < 23.5) error = 1;




	printUSB("Enter Upper Frequency in MHz: ");
	scanUSB(str1, 64);
	printUSB(str1);
	printUSB("\n");
	float upperFreq = (float) atof(str1);
	if (lowerFreq > 6000) error = 1;


	printUSB("Enter Sweep Time in Seconds: ");
	scanUSB(str1, 64);
	printUSB(str1);
	printUSB("\n");
	float sweepTime = (float) atof(str1);


	printUSB("Enter number of steps: ");
	scanUSB(str1, 64);
	printUSB(str1);
	printUSB("\n");
	uint16_t numSteps = atoi(str1);

	printUSB("Enter 'up' to sweep up frequencies, 'down' to sweep down, 'triangle' to do both: ");
	scanUSB(str1, 64);
	printUSB(str1);
	printUSB("\n");

	if (error)
	{
		printUSB("\nBad input, try harder next time.\n\n");
	}

	else if (strcmp(str1, "up") == 0 || strcmp(str1, "u") == 0)
	{
		while(1)
		{
			max2871Sweep(lowerFreq, upperFreq, numSteps, sweepTime, 1, max2871Status);
		}
	}

	else if (strcmp(str1, "down") == 0 || strcmp(str1, "d") == 0)
	{
		while(1)
		{
			max2871Sweep(lowerFreq, upperFreq, numSteps, sweepTime, 0, max2871Status);
		}
	}

	else if (strcmp(str1, "t") == 0 || strcmp(str1, "triangle") == 0)
	{
		while(1)
		{
			max2871Sweep(lowerFreq, upperFreq, numSteps, sweepTime, 1, max2871Status);
			max2871Sweep(lowerFreq, upperFreq, numSteps, sweepTime, 0, max2871Status);
		}
	}

	else
	{
		printUSB("\nBad input, try harder next time.\n\n");
	}

}
